codenocold/L-Stick/basic_group/test/main.c

#include "nrf_delay.h"
#include "nrf_log.h"
#include "nrf_log_ctrl.h"
#include "nrf_log_default_backends.h"

#include "systick.h"
#include "led.h"
#include "video.h"
#include "accel.h"
#include "dwt.h"
#include "key.h"
#include "power.h"
#include "storage.h"
#include "state_ctrl.h"
#include "light_mode.h"


static void key_loop(void);


int main(void)
{
    NRF_LOG_INIT(NULL);
    NRF_LOG_DEFAULT_BACKENDS_INIT();

    ACCEL_init();
    DWT_init();
    SYSTICK_init();
    LED_init();
    KEY_init(SYSTICK_get_tick);
    POWER_init();
    STORAGE_init();

    while (true){
        key_loop();
        STATE_CTRL_loop();
    }
}


static void key_loop(void)
{
    switch(KEY_scan()){
        case 1:     // Click
            if(POWER_is_locked()){
                LIGHT_MODE_index_next();
            }
            break;

        case 2:     // Double click
            if(POWER_is_locked()){
                LIGHT_MODE_index_prev();
            }
            break;

        case 3:     // Triple click
            STATE_CTRL_set_state(STATE_OFF_CHARG_COMPLETE);
            break;

        case 255:   // Long press
            if(POWER_is_locked()){
                // Power off
                STATE_CTRL_set_state(STATE_POWER_DOWN);
            }else{
                // Power on
                STATE_CTRL_set_state(STATE_POWER_UP);
            }
            break;

        default:
            break;
    }
}
