codenocold/L-Stick/basic_group/test/fastled.c

#include "fastled.h"


//----------------------------------------------------------------------------------
// Varable Definitions


//----------------------------------------------------------------------------------
// Function Declarations


void setLEDs(tRGB * leds, uint8_t num_leds, uint8_t r, uint8_t g, uint8_t b)
{
    for(int i=0; i<num_leds; i++){
        gLED[i].R = r;
        gLED[i].G = g;
        gLED[i].B = b;
    }
}

void stepToWhiteBy(tRGB * leds, uint8_t num_leds, uint8_t stepBy)
{
    for(int i = 0; i < num_leds; i++) { 
        rgb_scale(&leds[i], 255 + stepBy);
    }
}

void fadeToBlackBy( tRGB * leds, uint8_t num_leds, uint8_t fadeBy)
{
    for(int i = 0; i < num_leds; i++) { 
        rgb_scale(&leds[i], 255 - fadeBy);
    }
}

void addGlitter(uint8_t chanceOfGlitter, tRGB color) 
{
    uint8_t index;

    if( random8() < chanceOfGlitter) {
        index = random8() % LED_NUM;
        rgb_add(&gLED[index], color);
    }
}

tRGB ColorFromPalette( const tRGB *pal, uint8_t index, uint8_t brightness, tBlendType blendType)
{
    uint8_t hi4 = index >> 4;
    uint8_t lo4 = index & 0x0F;
    uint8_t hi4XsizeofCRGB = hi4 * sizeof(tRGB);

    // We then add that to a base array pointer.
    const tRGB* entry = (tRGB*)( (uint8_t*)(&(pal[0])) + hi4XsizeofCRGB);
    
    uint8_t blend = lo4 && (blendType != NOBLEND);
    
    uint8_t red1   = entry->R;
    uint8_t green1 = entry->G;
    uint8_t blue1  = entry->B;
    
    if( blend ) {
        if( hi4 == 15 ) {
            entry = &(pal[0]);
        } else {
            entry++;
        }
        
        uint8_t f2 = lo4 << 4;
        uint8_t f1 = 255 - f2;

        uint8_t red2   = entry->R;
        red1   = scale8( red1, f1);
        red2   = scale8( red2, f2);
        red1   += red2;

        uint8_t green2 = entry->G;
        green1 = scale8( green1, f1);
        green2 = scale8( green2, f2);
        green1 += green2;

        uint8_t blue2  = entry->B;
        blue1  = scale8( blue1, f1);
        blue2  = scale8( blue2, f2);
        blue1  += blue2;
    }
    
    if( brightness != 255) {
        if( brightness ) {
            brightness++;
            if( red1 )   {
                red1 = scale8( red1, brightness);
                red1++;
            }
            if( green1 ) {
                green1 = scale8( green1, brightness);
                green1++;
            }
            if( blue1 )  {
                blue1 = scale8( blue1, brightness);
                blue1++;
            }
        } else {
            red1 = 0;
            green1 = 0;
            blue1 = 0;
        }
    }
    
    tRGB rgb = {.R = red1, .G = green1, .B = blue1};

    return rgb;
}

void hsv2rgb(const tHSV * hsv, tRGB * rgb)
{
    // Yellow has a higher inherent brightness than
    // any other color; 'pure' yellow is perceived to
    // be 93% as bright as white.  In order to make
    // yellow appear the correct relative brightness,
    // it has to be rendered brighter than all other
    // colors.
    // Level Y1 is a moderate boost, the default.
    // Level Y2 is a strong boost.
    const uint8_t Y1 = 1;
    const uint8_t Y2 = 0;
    
    // G2: Whether to divide all greens by two.
    // Depends GREATLY on your particular LEDs
    const uint8_t G2 = 0;
    
    // Gscale: what to scale green down by.
    // Depends GREATLY on your particular LEDs
    const uint8_t Gscale = 0;
    
    uint8_t hue = hsv->H;
    uint8_t sat = hsv->S;
    uint8_t val = hsv->V;
    
    uint8_t offset = hue & 0x1F; // 0..31
    
    // offset8 = offset * 8
    uint8_t offset8 = offset;{
        // On ARM and other non-AVR platforms, we just shift 3.
        offset8 <<= 3;
    }
    
    uint8_t third = scale8( offset8, (256 / 3)); // max = 85
    
    volatile uint8_t r, g, b;
    
    if( ! (hue & 0x80) ) {
        // 0XX
        if( ! (hue & 0x40) ) {
            // 00X
            //section 0-1
            if( ! (hue & 0x20) ) {
                // 000
                //case 0: // R -> O
                r = 255 - third;
                g = third;
                b = 0;
            } else {
                // 001
                //case 1: // O -> Y
                if( Y1 ) {
                    r = 171;
                    g = 85 + third ;
                    b = 0;
                }
                if( Y2 ) {
                    r = 170 + third;
                    //uint8_t twothirds = (third << 1);
                    uint8_t twothirds = scale8( offset8, ((256 * 2) / 3)); // max=170
                    g = 85 + twothirds;
                    b = 0;
                }
            }
        } else {
            //01X
            // section 2-3
            if( !  (hue & 0x20) ) {
                // 010
                //case 2: // Y -> G
                if( Y1 ) {
                    //uint8_t twothirds = (third << 1);
                    uint8_t twothirds = scale8( offset8, ((256 * 2) / 3)); // max=170
                    r = 171 - twothirds;
                    g = 170 + third;
                    b = 0;
                }
                if( Y2 ) {
                    r = 255 - offset8;
                    g = 255;
                    b = 0;
                }
            } else {
                // 011
                // case 3: // G -> A
                r = 0;
                g = 255 - third;
                b = third;
            }
        }
    } else {
        // section 4-7
        // 1XX
        if( ! (hue & 0x40) ) {
            // 10X
            if( ! ( hue & 0x20) ) {
                // 100
                //case 4: // A -> B
                r = 0;
                //uint8_t twothirds = (third << 1);
                uint8_t twothirds = scale8( offset8, ((256 * 2) / 3)); // max=170
                g = 171 - twothirds; //170?
                b = 85  + twothirds;
                
            } else {
                // 101
                //case 5: // B -> P
                r = third;
                g = 0;
                b = 255 - third;
                
            }
        } else {
            if( !  (hue & 0x20)  ) {
                // 110
                //case 6: // P -- K
                r = 85 + third;
                g = 0;
                b = 171 - third;
                
            } else {
                // 111
                //case 7: // K -> R
                r = 170 + third;
                g = 0;
                b = 85 - third;
                
            }
        }
    }
    
    // This is one of the good places to scale the green down,
    // although the client can scale green down as well.
    if( G2 ) g = g >> 1;
    if( Gscale ) g = scale8_video( g, Gscale);
    
    // Scale down colors if we're desaturated at all
    // and add the brightness_floor to r, g, and b.
    if( sat != 255 ) {
        if( sat == 0) {
            r = 255; b = 255; g = 255;
        } else {
            if( r ) r = scale8_video( r, sat);
            if( g ) g = scale8_video( g, sat);
            if( b ) b = scale8_video( b, sat);

            uint8_t desat = 255 - sat;
            desat = scale8( desat, desat);
            
            uint8_t brightness_floor = desat;
            r += brightness_floor;
            g += brightness_floor;
            b += brightness_floor;
        }
    }
    
    // Now scale everything down if we're at value < 255.
    if( val != 255 ) {
        val = scale8_video( val, val);
        if( val == 0 ) {
            r=0; g=0; b=0;
        } else {
            if( r ) r = scale8_video( r, val);
            if( g ) g = scale8_video( g, val);
            if( b ) b = scale8_video( b, val);
        }
    }
    
    // Here we have the old AVR "missing std X+n" problem again
    // It turns out that fixing it winds up costing more than
    // not fixing it.
    // To paraphrase Dr Bronner, profile! profile! profile!
    //asm volatile(  ""  :  :  : "r26", "r27" );
    //asm volatile (" movw r30, r26 \n" : : : "r30", "r31");
    rgb->R = r;
    rgb->G = g;
    rgb->B = b;
}

uint8_t qadd8( uint8_t i, uint8_t j)
{
    unsigned int t = i + j;
    if( t > 255) t = 255;
    return t;
}

uint8_t qsub8( uint8_t i, uint8_t j)
{
    int t = i - j;
    if( t < 0)
        t = 0;
    return t;
}

uint8_t random8(void)
{
    static uint16_t rand16seed = 1337;
    rand16seed = (rand16seed * 2053) + 13849;
    return (uint8_t)(((uint8_t)(rand16seed & 0xFF)) + ((uint8_t)(rand16seed >> 8)));
}

uint8_t random8_1(uint8_t lim)
{
    uint8_t r = random8();
    r = (r*lim) >> 8;
    return r;
}

uint8_t random8_2(uint8_t min, uint8_t lim)
{
    uint8_t delta = lim - min;
    uint8_t r = random8_1(delta) + min;
    return r;
}

void rgb_scale(tRGB * rgb, uint16_t scale)
{
    uint16_t scale_fixed = scale + 1;
    uint16_t r = (((uint16_t)rgb->R) * scale_fixed) >> 8;
    uint16_t g = (((uint16_t)rgb->G) * scale_fixed) >> 8;
    uint16_t b = (((uint16_t)rgb->B) * scale_fixed) >> 8;

    if(scale_fixed > 0xFF){
        if(rgb->R == r) r++;
        if(rgb->G == g) g++;
        if(rgb->B == b) b++;
    }
   
    rgb->R = r > 255 ? 255 : r;
    rgb->G = g > 255 ? 255 : g;
    rgb->B = b > 255 ? 255 : b;
}

void rgb_nscale(tRGB * rgb, uint8_t num, uint8_t scale)
{
    for(int i=0; i<num; i++){
        rgb_scale(&rgb[i], scale);
    }
}

void rgb_add(tRGB * src_rgb, tRGB add_rgb)
{
    src_rgb->R = qadd8(src_rgb->R, add_rgb.R);
    src_rgb->G = qadd8(src_rgb->G, add_rgb.G);
    src_rgb->B = qadd8(src_rgb->B, add_rgb.B);
}

void rgb_sub(tRGB * src_rgb, tRGB sub_rgb)
{
    src_rgb->R = qsub8(src_rgb->R, sub_rgb.R);
    src_rgb->G = qsub8(src_rgb->G, sub_rgb.G);
    src_rgb->B = qsub8(src_rgb->B, sub_rgb.B);
}

void rgb_or(tRGB * src_rgb, tRGB rgb)
{
    if(src_rgb->R < rgb.R){
        src_rgb->R = rgb.R;
    }

    if(src_rgb->G < rgb.G){
        src_rgb->G = rgb.G;
    }

    if(src_rgb->B < rgb.B){
        src_rgb->B = rgb.B;
    }
}

uint16_t beat8( uint16_t beats_per_minute_88, uint32_t timebase)
{
    return ((SYSTICK_get_tick() - timebase) * beats_per_minute_88 * 280) >> 16;
}

uint16_t beat16( uint16_t beats_per_minute, uint32_t timebase)
{
    // Convert simple 8-bit BPM's to full Q8.8 accum88's if needed
    if( beats_per_minute < 256) beats_per_minute <<= 8;
    return beat8(beats_per_minute, timebase);
}

uint8_t beatsin8( uint16_t beats_per_minute, uint8_t lowest, uint8_t highest, uint32_t timebase, uint8_t phase_offset)
{
    uint8_t beat = beat16( beats_per_minute, timebase) >> 8;
    uint8_t beatsin = sin8( beat + phase_offset);
    uint8_t rangewidth = highest - lowest;
    uint8_t scaledbeat = scale8( beatsin, rangewidth);
    uint8_t result = lowest + scaledbeat;
    return result;
}

uint16_t beatsin16( uint16_t beats_per_minute, uint16_t lowest, uint16_t highest, uint32_t timebase, uint16_t phase_offset)
{
    uint16_t beat = beat16( beats_per_minute, timebase);
    uint16_t beatsin = (sin16( beat + phase_offset) + 32768);
    uint16_t rangewidth = highest - lowest;
    uint16_t scaledbeat = scale16( beatsin, rangewidth);
    uint16_t result = lowest + scaledbeat;
    return result;
}

uint8_t sin8( uint8_t theta)
{
    const uint8_t b_m16_interleave[] = { 0, 49, 49, 41, 90, 27, 117, 10 };

    uint8_t offset = theta;
    if( theta & 0x40 ) {
        offset = (uint8_t)255 - offset;
    }
    offset &= 0x3F; // 0..63

    uint8_t secoffset  = offset & 0x0F; // 0..15
    if( theta & 0x40) secoffset++;

    uint8_t section = offset >> 4; // 0..3
    uint8_t s2 = section * 2;
    const uint8_t* p = b_m16_interleave;
    p += s2;
    uint8_t b   =  *p;
    p++;
    uint8_t m16 =  *p;

    uint8_t mx = (m16 * secoffset) >> 4;

    int8_t y = mx + b;
    if( theta & 0x80 ) y = -y;

    y += 128;

    return y;
}

int16_t sin16( uint16_t theta )
{
    static const uint16_t base[] =
    { 0, 6393, 12539, 18204, 23170, 27245, 30273, 32137 };
    static const uint8_t slope[] =
    { 49, 48, 44, 38, 31, 23, 14, 4 };

    uint16_t offset = (theta & 0x3FFF) >> 3; // 0..2047
    if( theta & 0x4000 ) offset = 2047 - offset;

    uint8_t section = offset / 256; // 0..7
    uint16_t b   = base[section];
    uint8_t  m   = slope[section];

    uint8_t secoffset8 = (uint8_t)(offset) / 2;

    uint16_t mx = m * secoffset8;
    int16_t  y  = mx + b;

    if( theta & 0x8000 ) y = -y;

    return y;
}
