codenocold/L-Stick/basic_group/test/storage_default.c

#include "storage.h"
#include "light_mode.h"


volatile tModeTable DefaultModeTable __attribute__ ((section(".mode_table"))) = {
    {

		LM_VIDEO_0,			// 0
		LM_VIDEO_1,			// 1
		LM_VIDEO_2,			// 2
		LM_VIDEO_3,			// 3
		LM_VIDEO_4,			// 4
		LM_VIDEO_5,			// 5
		LM_VIDEO_6,			// 6
        LM_VIDEO_7,			// 7
        LM_VIDEO_8,			// 8
        LM_BIKE_0,			// 9
        LM_STATIC_LIGHT_0,			// 10
        LM_STATIC_LIGHT_1,			// 11
        LM_NULL,			// 12
        LM_NULL,			// 13
        LM_NULL,			// 14
        LM_NULL,			// 15
    }
};

volatile tStaticLight DefaultStaticLight __attribute__ ((section(".static_light"))) = {
	{
	    {50,0,0,},
	    {0,50,0,},
	    {0,0,50,},
	    {50,50,0,},
	    {0,50,50,},
	    {50,0,50,},
	}
};

volatile unsigned char DefaultIMG0[4*48*16] __attribute__ ((section(".img0"))) = {
	0xFF, 0x01, 0x01, 0x00, 0xFF, 0x01, 0x01, 0x00, 0xFF, 0x01, 0x01, 0x00, 0xFF, 0x01, 0x01, 0x00, 0xFF, 0x01, 0x01, 0x00, 0xFF, 0x01, 0x01, 0x00, 0xFF, 0x01, 0x01, 0x00, 0xFF, 0x01, 0x01, 0x00, 0xFF, 0x01, 0x01, 0x00, 0xFF, 0x01, 0x01, 0x00, 0xFF, 0x01, 0x01, 0x00, 0xFF, 0x01, 0x01, 0x00, 0xFF, 0x01, 0x01, 0x00, 0xFF, 0x01, 0x01, 0x00, 0xFF, 0x01, 0x01, 0x00, 0xFF, 0x01, 0x01, 0x00, 
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
};
